jsain78480/2324_Projet3DN_AnalyseurQualiteReseauElectrique/Software/Projet_Analyseur_Reseau/Core/Inc/oled_fonts.h

/*
 * oled_fonts.h
 *
 *  Created on: May 17, 2024
 *      Author: jingwen.zhang
 */


#include <stdint.h>

#ifndef INC_OLED_FONTS_H_
#define INC_OLED_FONTS_H_

#define SSD1306_INCLUDE_FONT_6x8
#define SSD1306_INCLUDE_FONT_7x10
#define SSD1306_INCLUDE_FONT_11x18
#define SSD1306_INCLUDE_FONT_16x26
#define SSD1306_INCLUDE_FONT_16x24

#include "oled_fonts.h"


typedef struct {
	const uint8_t FontWidth;    /*!< Font width in pixels */
	uint8_t FontHeight;   /*!< Font height in pixels */
	const uint16_t *data; /*!< Pointer to data font data array */
} FontDef;


#ifdef SSD1306_INCLUDE_FONT_6x8
extern FontDef Font_6x8;
#endif
#ifdef SSD1306_INCLUDE_FONT_7x10
extern FontDef Font_7x10;
#endif
#ifdef SSD1306_INCLUDE_FONT_11x18
extern FontDef Font_11x18;
#endif
#ifdef SSD1306_INCLUDE_FONT_16x26
extern FontDef Font_16x26;
#endif
#ifdef SSD1306_INCLUDE_FONT_16x24
extern FontDef Font_16x24;
#endif


#endif /* INC_OLED_FONTS_H_ */
